studiohsoftware/2WIRELESS/Firmware/photon/PhotonCore/softap.cpp

#include <cstdlib>
#include <algorithm>
#include "wiced.h"
#include "http_server.h"
#include "static_assert.h"
#include "dns_redirect.h"
#include "wiced_security.h"
#include "jsmn.h"
#include "softap.h"
#include "softap_http.h"
#include "dct.h"
#include "ota_flash_hal.h"
#include "spark_protocol_functions.h"
#include "spark_macros.h"
#include "core_hal.h"
#include "rng_hal.h"
#include "ota_flash_hal_stm32f2xx.h"
#include "bytes2hexbuf.h"
#include "spark_wiring_wifi_credentials.h"
#include "mbedtls/aes.h"
#include "device_code.h"
//2WIRELESS
#include "wwd_sdpcm.h"
#include "wwd_wlioctl.h"
#include "wwd_ap_common.h"
#include "rtos.h"
#include "wwd_rtos_interface.h"

#if SOFTAP_HTTP
# include "http_server.h"

# ifndef SOFTAP_HTTP_MAXIMUM_CONNECTIONS
#  define SOFTAP_HTTP_MAXIMUM_CONNECTIONS (10)
# endif // SOFTAP_HTTP_MAXIMUM_CONNECTIONS

# define SOFTAP_HTTP_MAXIMUM_URL_LENGTH 255
#endif // SOFTAP_HTTP

//2WIRELESS
static host_semaphore_type_t wwd_wifi_sleep_flag;

extern WLanSecurityType toSecurityType(wiced_security_t sec);

//2WIRELESS
wwd_result_t disable_ssid_broadcast(int disable)
{
    wiced_buffer_t buffer;
    uint32_t*      data;

	/* Make the AP "hidden" */
	data = (uint32_t*) wwd_sdpcm_get_iovar_buffer( &buffer, (uint16_t) 4, IOVAR_STR_CLOSEDNET );
	CHECK_IOCTL_BUFFER_WITH_SEMAPHORE( data, &wwd_wifi_sleep_flag );
	data[0] = (uint32_t) disable;
	CHECK_RETURN_WITH_SEMAPHORE( wwd_sdpcm_send_iovar( SDPCM_SET, buffer, 0, WWD_AP_INTERFACE ), &wwd_wifi_sleep_flag );
	return WWD_SUCCESS;
}

// This is a copy-paste from spark_wiring_json.h
static size_t json_unescape(char *json, size_t len) {
    char *str = json; // Destination string
    const char* const end = json + len; // End of the source string
    const char *s1 = str; // Beginning of an unescaped sequence
    const char *s = s1;
    while (s != end) {
        if (*s == '\\') {
            if (s != s1) {
                const size_t n = s - s1;
                memmove(str, s1, n); // Shift preceeding characters
                str += n;
                s1 = s;
            }
            ++s;
            if (s == end) {
                return false; // Unexpected end of string
            }
            // if (*s == 'u') { // Arbitrary character, e.g. "\u001f"
            //     ++s;
            //     if (end - s < 4) {
            //         return false; // Unexpected end of string
            //     }
            //     uint32_t u = 0; // Unicode code point or UTF-16 surrogate pair
            //     if (!hexToInt(s, 4, &u)) {
            //         return false; // Invalid escaped sequence
            //     }
            //     if (u <= 0x7f) { // Processing only code points within the basic latin block
            //         *str = u;
            //         ++str;
            //         s1 += 6; // Skip escaped sequence
            //     }
            //     s += 4;
            // } else {
                switch (*s) {
                case '"':
                case '\\':
                case '/':
                    *str = *s;
                    break;
                case 'b': // Backspace
                    *str = 0x08;
                    break;
                case 't': // Tab
                    *str = 0x09;
                    break;
                case 'n': // Line feed
                    *str = 0x0a;
                    break;
                case 'f': // Form feed
                    *str = 0x0c;
                    break;
                case 'r': // Carriage return
                    *str = 0x0d;
                    break;
                default:
                    return false; // Invalid escaped sequence
                }
                ++str;
                ++s;
                s1 = s; // Skip escaped sequence
            // }
        } else {
            ++s;
        }
    }
    if (s != s1) {
        const size_t n = s - s1;
        memmove(str, s1, n); // Shift remaining characters
        str += n;
    }
    return (str - json); // Update string length
}

int resolve_dns_query(const char* query, const char* table)
{
    int result = 0;
    while (*table!=0xFF && *table)
    {
        unsigned len = strlen(table)+1;
        if (!memcmp(query, table, len))
        {
            result = len;
            break;
        }
        table += len;
    }
    return result;
}

/**
 * Override resolution.
 * @param query
 * @return
 */
int dns_resolve_query(const char* query)
{
    int result = dns_resolve_query_default(query);
    if (result<=0)
    {
        const char* valid_queries = (const char*) dct_read_app_data_lock(DCT_DNS_RESOLVE_OFFSET);
        result = resolve_dns_query(query, valid_queries);
        dct_read_app_data_unlock(DCT_DNS_RESOLVE_OFFSET);
    }
    return result;
}

bool is_device_claimed()
{
	return HAL_IsDeviceClaimed(nullptr);
}


/**
 * A command that consumes data from a reader and produces a result to a writer.
 */
class Command {

public:
    /**
     * Executes this command.
     * @param reader    The data supplied to the command.
     * @param writer    The writer that receives the result of the command.
     * @return  A command response code. By convention 0 indicates success.
     */
    virtual int execute(Reader& reader, Writer& writer)=0;
};

/**
 * Base class for commands whose requests and responses are encoded using
 * json.
 */
class JSONCommand : public Command {

protected:

    jsmntok_t * json_tokenise(char *js)
    {
        jsmn_parser parser;
        parser.size = sizeof(parser);
        jsmn_init(&parser, NULL);

        unsigned int n = 64;
        jsmntok_t* tokens = (jsmntok_t*)malloc(sizeof(jsmntok_t) * n);
        if (!tokens) return nullptr;
        int ret = jsmn_parse(&parser, js, strlen(js), tokens, n, NULL);
        while (ret==JSMN_ERROR_NOMEM)
        {
            n = n * 2 + 1;
            jsmntok_t* prev = tokens;
            tokens = (jsmntok_t*)realloc(tokens, sizeof(jsmntok_t) * n);
            if (!tokens) {
            		free(prev);
            		return nullptr;
            }
            ret = jsmn_parse(&parser, js, strlen(js), tokens, n, NULL);
        }
        return tokens;
    }

    bool json_token_streq(const char *js, jsmntok_t *t, const char *s)
    {
        return (strncmp(js + t->start, s, t->end - t->start) == 0
                && strlen(s) == (size_t) (t->end - t->start));
    }

    char* json_token_tostr(char *js, jsmntok_t *t)
    {
        js[t->end] = '\0';
        return js + t->start;
    }

    void write_result_code(Writer& writer, int result) {
        write_char(writer, '{');
        write_json_int(writer, "r", result);
        write_char(writer, '}');
    }

    virtual int parse_request(Reader& reader) { return 0; }

    virtual void produce_response(Writer& writer, int result) {
        write_result_code(writer, result);
    }

    /**
     * The core processing for this command. Consumes the request object and produces
     * the response.
     * @return The command result code to return from execute().
     */
    virtual int process() { return 0; }

    void write_char(Writer& w, char c) {
        w.write((uint8_t*)&c, 1);
    }

    void write_quoted_string(Writer& out, const char* s) {
        write_char(out, '"');
        out.write(s);
        write_char(out, '"');
    }

    void write_json_string(Writer& out, const char* name, const char* value) {
        write_quoted_string(out, name);
        write_char(out, ':');
        write_quoted_string(out, value);
    }

    char* int_to_ascii(int val, char* buf, int i) {
        buf[--i] = 0;
        bool negative = val < 0;
        if (negative) {
            val = -val;
        }
        buf[--i] = (val % 10) + '0';
        val /= 10;
        for(; val && i ; val /= 10) {
            buf[--i] = (val % 10) + '0';
        }
        if (negative)
            buf[--i] = '-';
        return &buf[i];
    }

    void write_json_int(Writer& out, const char* name, int value) {
        char buf[20];
        write_quoted_string(out, name);
        write_char(out, ':');
        out.write(int_to_ascii(value, buf, 20));
    }

public:

    virtual int execute(Reader& reader, Writer& writer)
    {
        int result = parse_request(reader);
        if (!result) {
            result = process();
            produce_response(writer, result);
        }
        return result;
    }
};


#define JSON_DEBUG(x)

/**
 * A command that parses a JSON request.
 */

class JSONRequestCommand : public JSONCommand {

protected:

	/**
	 * Template method allowing subclasses to handle the parsed json keys.
	 * @param index The index into the array of keys passed to parse_json_requet of the key that has been matched.
	 */
    virtual bool parsed_key(unsigned index)=0;

    /**
     * Template methods allowing subclasses to handle the parsed JSON values.
     * @param index	the key index this value belongs to
     * @param t		the jsmn token
     * @param value	The string value.
     *
     * Note that the t and value parameters have a lifetime only for the duration of the method.
     * They should not be stored for later use.
     */
    virtual bool parsed_value(unsigned index, jsmntok_t* t, char* value)=0;

    int parse_json_request(Reader& reader, const char* const keys[], const jsmntype_t types[], unsigned count) {

        int result = -1;
    		char* js = reader.fetch_as_string();
        if (js)
        {
			jsmntok_t *tokens = json_tokenise(js);
			if (tokens)
			{
				enum parse_state { START, KEY, VALUE, SKIP, STOP };

				parse_state state = START;
				jsmntype_t expected_type = JSMN_OBJECT;

				result = 0;
				int key = -1;

				for (size_t i = 0, j = 1; j > 0; i++, j--)
				{
					jsmntok_t *t = &tokens[i];
					if (t->type == JSMN_ARRAY || t->type == JSMN_OBJECT)
						j += t->size * 2;

					switch (state)
					{
						case START:
							state = KEY;
							break;

						case KEY:
							state = VALUE;
							key = -1;
							for (size_t i = 0; i < count; i++)
							{
								if (json_token_streq(js, t, keys[i]))
								{
									expected_type = types[i];
									if (parsed_key(i)) {
										key = i;
										JSON_DEBUG( ( "key: %s %d %d\n", keys[i], i, (int)expected_type ) );
									}
								}
							}
							if (key==-1) {
								JSON_DEBUG( ( "unknown key: %s\n", json_token_tostr(js, t) ) );
								result = -1;
							}
							break;

						case VALUE:
							if (key!=-1) {
								if (t->type != expected_type) {
									result = -1;
									JSON_DEBUG( ( "type mismatch\n" ) );
								}
								else {
									char *str = json_token_tostr(js, t);
									if (!parsed_value(key, t, str))
										result = -1;
								}
							}
							state = KEY;
							break;

						case STOP: // Just consume the tokens
							break;

						default:
							result = -1;
					}
				}
				free(tokens);
			}
			free(js);
        }
        return result;
    }
};


class VersionCommand : public JSONCommand {

public:
    void produce_response(Writer& out, int result) {
        out.write("{\"v\":2}");
    }
};

struct ScanEntry {
    char ssid[33];
    uint8_t done;
    int32_t rssi;
    int32_t security;
    int32_t channel;
    int32_t max_data_rate;
};

class ScanAPCommand : public JSONCommand {
    wiced_queue_t queue_;

    // these can be quite large, so allocate on the heap
    ScanEntry read_;
    ScanEntry write_;

public:
    ScanAPCommand()
    {
    }

    /**
     * Initializes the scan queue, and start a scan using the WICED wifi scan api.
     *
     */
    int process() {
        int result = wiced_rtos_init_queue(&queue_, NULL, sizeof(ScanEntry), 5);
        if (!result) {
            result = wiced_wifi_scan_networks(scan_handler, this);
            if (result)
                wiced_rtos_deinit_queue(&queue_);
        }
        return result;
    }

    void produce_response(Writer& out, const int result) {
        out.write("{\"scans\":[");
        bool first = true;
        ScanEntry& entry = read_;
        while (!result && !wiced_rtos_pop_from_queue(&queue_, &entry, WICED_NEVER_TIMEOUT)) {
            if (entry.done)
                break;
            if (!*entry.ssid)
                continue;
            if (first)
                first = false;
            else
                write_char(out, ',');
            write_char(out, '{');
            write_json_string(out, "ssid", entry.ssid);
            write_char(out, ',');
            write_json_int(out, "rssi", entry.rssi);
            write_char(out, ',');
            write_json_int(out, "sec", entry.security);
            write_char(out, ',');
            write_json_int(out, "ch", entry.channel);
            write_char(out, ',');
            write_json_int(out, "mdr", entry.max_data_rate);
            write_char(out, '}');
        }
        out.write("]}");
        wiced_rtos_deinit_queue(&queue_);
    }

    static wiced_result_t scan_handler(wiced_scan_handler_result_t* malloced_scan_result)
    {
        ScanAPCommand& cmd = *(ScanAPCommand*)malloced_scan_result->user_data;
        malloc_transfer_to_curr_thread( malloced_scan_result );
        ScanEntry& entry = cmd.write_;
        memset(&entry, 0, sizeof(entry));
        if (malloced_scan_result->status == WICED_SCAN_INCOMPLETE)
        {
            wiced_scan_result_t& ap_details = malloced_scan_result->ap_details;
            unsigned ssid_len = ap_details.SSID.length > 32 ? 32 : ap_details.SSID.length;
            memcpy(entry.ssid, ap_details.SSID.value, ssid_len);
            entry.ssid[ssid_len] = 0;
            entry.rssi = ap_details.signal_strength;
            entry.security = ap_details.security;
            entry.channel = ap_details.channel;
            entry.max_data_rate = ap_details.max_data_rate;
        }
        else
        {
            entry.done = 1;
        }
        wiced_rtos_push_to_queue(&cmd.queue_, &entry, WICED_WAIT_FOREVER);
        free(malloced_scan_result);
        return WICED_SUCCESS;
    }
};

struct ConfigureAP {
    int32_t index;
    char ssid[33];
    char passcode[65];
    int32_t security;
    int32_t channel;
};


uint8_t hex_nibble(unsigned char c) {
    if (c<'0')
        return 0;
    if (c<='9')
        return c-'0';
    if (c<='Z')
        return c-'A'+10;
    if (c<='z')
        return c-'a'+10;
    return 0;
}

size_t hex_decode(uint8_t* buf, size_t len, const char* hex) {
    unsigned char c = '0'; // any non-null character
    size_t i;
    for (i=0; i<len && c; i++) {
        uint8_t b;
        if (!(c = *hex++))
            break;
        b = hex_nibble(c)<<4;
        if (c) {
            c = *hex++;
            b |= hex_nibble(c);
        }
        *buf++ = b;
    }
    return i;
}

/**
 *
 * @param hex_encoded   The hex_encoded encrypted data
 * The plaintext is stored in hex_encoded
 */
int decrypt(char* plaintext, int max_plaintext_len, char* hex_encoded_ciphertext) {
    const size_t len = 256;
    uint8_t buf[len];
    hex_decode(buf, len, hex_encoded_ciphertext);

    // reuse the hex encoded buffer
    const uint8_t *key = fetch_device_private_key(1); // fetch and lock private key data
    int plaintext_len = decrypt_rsa(buf, key, (uint8_t*)plaintext, max_plaintext_len);
    fetch_device_private_key(0); // unlock private key data
    return plaintext_len;
}

/**
 * Connects to an access point using the given credentials and signals
 * soft-ap process complete.
 */
class ConfigureAPCommand : public JSONRequestCommand {

	/**
	 * Receives the data from parsing the json.
	 */
    spark::WiFiAllocatedCredentials credentials;

    static const char* KEY[12];
    static const int OFFSET[];
    static const jsmntype_t TYPE[];

    std::unique_ptr<char[]> ekey_;

    int decrypt_result;

    int save_credentials() {
        WLanCredentials creds = credentials.getHalCredentials();
        if (creds.private_key && creds.private_key_len) {
            creds.private_key_len = decrypt_private_key(creds.private_key, creds.private_key_len);
        }
        return decrypt_result<0 ? decrypt_result :
            wlan_set_credentials(&creds);
    }

protected:

    virtual bool parsed_key(unsigned index) {
        return true;
    }

    int decrypt_private_key(const uint8_t* pkey, int len) {
        if (!(ekey_ && pkey && len))
            return 0;

        const size_t block_size = 16;
        uint8_t buf[block_size];
        const uint8_t* key = (const uint8_t*)ekey_.get();
        uint8_t* iv = (uint8_t*)ekey_.get() + block_size;

        mbedtls_aes_context ctx = {0};
        mbedtls_aes_setkey_dec(&ctx, key, 128);

        uint8_t* bptr = (uint8_t*)pkey;

        for (uint8_t* ptr = (uint8_t*)pkey; ptr - pkey < len; ptr += block_size * 2) {
            hex_decode(buf, block_size, (const char*)ptr);
            mbedtls_aes_crypt_cbc(&ctx, MBEDTLS_AES_DECRYPT, block_size, iv, buf, bptr);
            bptr += block_size;
        }

        decrypt_result = 1;

        return (len / 2);
        }

    virtual bool parsed_value(unsigned key, jsmntok_t* t, char* str) {
        std::unique_ptr<char[]> tmp;
        switch(key) {
            case 0:
            // idx
            break;
            case 1:
            // ssid
            if (t->type == JSMN_STRING) {
                credentials.setSsid(str);
            }
            break;
            case 2:
            // pwd
            if (t->type == JSMN_STRING) {
#define USE_PWD_ENCRYPTION 1
#if USE_PWD_ENCRYPTION
                size_t len = strlen(str);
                if (len / 2) {
                    tmp.reset(new (std::nothrow) char[len / 2 + 1]);
                    if (tmp) {
                        memset(tmp.get(), 0, len / 2 + 1);
                        decrypt_result = decrypt((char*)tmp.get(), len, str);
                        JSON_DEBUG( ( "Decrypted password %s\n", (char*)tmp));
                        str = tmp.get();
                    }
                }
#endif
                credentials.setPassword(str);
        }
            break;
            case 3:
            // ch
            credentials.setChannel(atoi(str));
            break;
            case 4:
            // sec
            // Why are we receiving WICED-specific security type here?
            credentials.setSecurity((WLanSecurityType)toSecurityType((wiced_security_t)atoi(str)));
            break;
            case 5:
            // eap
            credentials.setEapType((WLanEapType)atoi(str));
            break;
            case 6:
            // outer identity
            if (t->type == JSMN_STRING) {
                credentials.setOuterIdentity(str);
        }
            break;
            case 7:
            // inner identity
            if (t->type == JSMN_STRING) {
                credentials.setInnerIdentity(str);
            }
            break;
            case 8:
            // certificate
            if (t->type == JSMN_STRING) {
                size_t len = json_unescape(str, strlen(str));
                credentials.setClientCertificate((const uint8_t*)str, len + 1);
            }
            break;
            case 9:
            // encryption key
            if (t->type == JSMN_STRING) {
                size_t len = strlen(str);
                if (len / 2) {
                    tmp.reset(new (std::nothrow) char[len / 2 + 1]);
                    if (tmp) {
                        memset(tmp.get(), 0, len / 2 + 1);
                        decrypt_result = decrypt((char*)tmp.get(), len, str);
                        ekey_ = std::move(tmp);
                    }
                }
            }
            break;
            case 10:
            // private key
            if (t->type == JSMN_STRING) {
                size_t len = strlen(str);
                credentials.setPrivateKey((const uint8_t*)str, len + 1);
                // Just in case set the password as well, as there is a check somewhere that will
                // set security to Open if there is no password.
                credentials.setPassword("1");
            }
            break;
            case 11:
            // root ca
            if (t->type == JSMN_STRING) {
                size_t len = json_unescape(str, strlen(str));
                credentials.setRootCertificate((const uint8_t*)str, len + 1);
            }
            break;
        }
        return true;
    }

    int parse_request(Reader& reader) {
        decrypt_result = 0;
        credentials.reset();
        return parse_json_request(reader, KEY, TYPE, arraySize(KEY));
    }

    /**
     * Write the requested AP details to DCT
     * @return
     */
    int process() {
        return save_credentials();
    }

};

const char* ConfigureAPCommand::KEY[12] = {"idx","ssid","pwd","ch","sec",
                                           "eap","oi","ii","crt","ek","key","ca"};
const jsmntype_t ConfigureAPCommand::TYPE[] = { JSMN_PRIMITIVE, JSMN_STRING, JSMN_STRING,
                                                JSMN_PRIMITIVE, JSMN_PRIMITIVE, JSMN_PRIMITIVE,
                                                JSMN_STRING, JSMN_STRING, JSMN_STRING,
                                                JSMN_STRING, JSMN_STRING, JSMN_STRING };


class ConnectAPCommand : public JSONCommand {
    int index;
    wiced_semaphore_t* signal_complete_;
    void (*softap_complete_)();
    int responseCode;
public:
    ConnectAPCommand(wiced_semaphore_t* signal_complete, void (*softap_complete)()) {
        signal_complete_ = signal_complete;
        softap_complete_ = softap_complete;
    }

protected:
    // todo - parse index

    int process() {
        int result = 1;
        if (signal_complete_!=NULL) {
            wiced_rtos_set_semaphore(signal_complete_);
            result = 0;
        }
        return result;
    }

    void produce_response(Writer& writer, int result) {
        write_result_code(writer, result);
        if (softap_complete_)
            softap_complete_();
    }
};

class DeviceIDCommand : public JSONCommand {

    char device_id[25];

public:
    DeviceIDCommand() {}

    static void get_device_id(char buffer[25]) {
        bytes2hexbuf((const uint8_t*)0x1FFF7A10, 12, buffer);
        buffer[24] = 0;
    }

protected:
    int process() {
        memset(device_id, 0, sizeof(device_id));
        get_device_id(device_id);
        return 0;
    }

    void produce_response(Writer& writer, int result) {
        write_char(writer, '{');
        write_json_string(writer, "id", device_id);
        write_char(writer, ',');
        write_json_string(writer, "c", is_device_claimed() ? "1" : "0");
        write_char(writer, '}');
    }
};

class PublicKeyCommand : public JSONCommand {

protected:

    int process() {
        return 0;
    }

    void produce_response(Writer& writer, int result) {
        // fetch public key
        const int length = EXTERNAL_FLASH_SERVER_PUBLIC_KEY_LENGTH;
        const uint8_t* data = fetch_device_public_key(1); // fetch and lock public key data
        write_char(writer, '{');
        if (data) {
            writer.write("\"b\":\"");
            for (unsigned i=length; i-->0; ) {
                uint8_t v = *data++;
                write_char(writer, ascii_nibble(v>>4));
                write_char(writer, ascii_nibble(v&0xF));
            }
            write_char(writer, '"');
            write_char(writer, ',');
        }
        else {
            result = 1;
        }

        fetch_device_public_key(0); // unlock public key data

        write_json_int(writer, "r", result);
        write_char(writer, '}');
    }
};


class SetValueCommand  : public JSONRequestCommand {

	static const unsigned MAX_KEY_LEN = 3;
	static const unsigned MAX_VALUE_LEN = 64;

    static const char* const KEY[2];
    static const jsmntype_t TYPE[2];

    char key[MAX_KEY_LEN+1];
    char value[MAX_VALUE_LEN+1];

protected:

    virtual bool parsed_key(unsigned index) {
        return true;
    }

    inline void assign(char* target, const char* value, unsigned len) {
    		strncpy(target, value, len);
    		target[len-1] = '\0';
    }

    virtual bool parsed_value(unsigned index, jsmntok_t* t, char* value) {
        if (index==0)     // key
        		assign(this->key, value, MAX_KEY_LEN);
        else
        		assign(this->value, value, MAX_VALUE_LEN);
        return true;
    }

    int parse_request(Reader& reader) {
        key[0] = 0; value[0] = 0;
        return parse_json_request(reader, KEY, TYPE, arraySize(KEY));
    }

    int process() {
        int result = -1;
        if (*key && *value) {
            if (!strcmp(key,"cc")) {
                result = HAL_Set_Claim_Code(value);
            }
        }
        return result;
    }
};

const char* const SetValueCommand::KEY[2] = { "k", "v" };
const jsmntype_t SetValueCommand::TYPE[2] = { JSMN_STRING, JSMN_STRING };

struct AllSoftAPCommands {
    VersionCommand version;
    DeviceIDCommand deviceID;
    ScanAPCommand scanAP;
    ConfigureAPCommand configureAP;
    ConnectAPCommand connectAP;
    PublicKeyCommand publicKey;
    SetValueCommand setValue;
    AllSoftAPCommands(wiced_semaphore_t* complete, void (*softap_complete)()) :
        connectAP(complete, softap_complete) {}
};

const int MAX_SSID_PREFIX_LEN = 25;

bool fetch_or_generate_ssid_prefix(device_code_t* SSID) {
    const uint8_t* prefix = (const uint8_t*)dct_read_app_data_lock(DCT_SSID_PREFIX_OFFSET);
    uint8_t len = *prefix;
    bool generate = (!len || len>MAX_SSID_PREFIX_LEN);
    if (generate) {
        dct_read_app_data_unlock(DCT_SSID_PREFIX_OFFSET);
        strcpy((char*)SSID->value, "Photon");
        SSID->length = 6;
        dct_write_app_data(SSID, DCT_SSID_PREFIX_OFFSET, SSID->length+1);
    }
    else {
        memcpy(SSID, prefix, DCT_SSID_PREFIX_SIZE);
        dct_read_app_data_unlock(DCT_SSID_PREFIX_OFFSET);
    }
    if (SSID->length>MAX_SSID_PREFIX_LEN)
        SSID->length = MAX_SSID_PREFIX_LEN;
    return generate;
}

extern "C" wiced_ip_setting_t device_init_ip_settings;

/**
 * Manages the soft access point.
 */
class SoftAPController {
    wiced_semaphore_t complete;
    dns_redirector_t dns_redirector;

    wiced_result_t setup_soft_ap_credentials() {

        wiced_config_soft_ap_t expected;
        memset(&expected, 0, sizeof(expected));
        fetch_or_generate_setup_ssid((device_code_t*)&expected.SSID);

        expected.channel = 11;
        expected.details_valid = WICED_TRUE;

        wiced_config_soft_ap_t* soft_ap;
        wiced_result_t result = wiced_dct_read_lock( (void**) &soft_ap, WICED_FALSE, DCT_WIFI_CONFIG_SECTION, OFFSETOF(platform_dct_wifi_config_t, soft_ap_settings), sizeof(wiced_config_soft_ap_t) );
        if (result == WICED_SUCCESS)
        {
            if (memcmp(&expected, soft_ap, sizeof(expected))) {
                wiced_dct_read_unlock( soft_ap, WICED_FALSE );
                result = wiced_dct_write(&expected, DCT_WIFI_CONFIG_SECTION, OFFSETOF(platform_dct_wifi_config_t, soft_ap_settings), sizeof(wiced_config_soft_ap_t));
            } else {
                wiced_dct_read_unlock( soft_ap, WICED_FALSE );
            }
        }
		
        return result;
    }

public:

    wiced_semaphore_t& complete_semaphore() {
        return complete;
    }

    wiced_result_t start() {
        wiced_result_t result;
        if (!(result=wiced_rtos_init_semaphore(&complete)))
            if (!(result=setup_soft_ap_credentials()))
                if (!(result=wiced_network_up( WICED_AP_INTERFACE, WICED_USE_INTERNAL_DHCP_SERVER, &device_init_ip_settings )))
                    if (!(result=wiced_dns_redirector_start( &dns_redirector, WICED_AP_INTERFACE )))
                        result = WICED_SUCCESS;
        return result;
    }

    void waitForComplete() {
        wiced_rtos_get_semaphore(&complete, WICED_WAIT_FOREVER);
    }

    void signalComplete() {
        wiced_rtos_set_semaphore(&complete);
    }

    void stop() {

        /* Cleanup DNS server */
        wiced_dns_redirector_stop(&dns_redirector);

        /* Turn off AP */
        wiced_network_down( WICED_AP_INTERFACE );

        signalComplete();
        wiced_rtos_deinit_semaphore(&complete);
    }
};

class Dispatcher {
public:
    void start() {};
    void stop() {};
};

static void tcp_write(Writer* w, const uint8_t *buf, size_t count) {
    wiced_tcp_stream_t* tcp_stream = (wiced_tcp_stream_t*)w->state;
    wiced_tcp_stream_write(tcp_stream, buf, count);
}

static int tcp_read(Reader* r, uint8_t *buf, size_t count) {
    wiced_tcp_stream_t* tcp_stream = (wiced_tcp_stream_t*)r->state;
    int result = wiced_tcp_stream_read(tcp_stream, buf, count, WICED_NEVER_TIMEOUT);
    return result==WICED_SUCCESS ? count : (result < 0 ? result : -result);
}

static void tcp_stream_writer(Writer& w, wiced_tcp_stream_t* stream) {
    w.callback = tcp_write;
    w.state = stream;
}

static void tcp_stream_reader(Reader& r, wiced_tcp_stream_t* stream) {
    r.bytes_left = SIZE_MAX;
    r.callback = tcp_read;
    r.state = stream;
}

int read_from_buffer(Reader* r, uint8_t* target, size_t length) {
    memcpy(target, r->state, length);
    r->state = ((uint8_t*)r->state)+length;
    return length;
}

void reader_from_buffer(Reader* r, const uint8_t* buffer, size_t length)
{
    r->bytes_left = length;
    r->callback = read_from_buffer;
    r->state = (void*)buffer;
}


void cleanup_http_body(wiced_http_message_body_t* body)
{
    if (body->user)
    {
        wiced_packet_delete((wiced_packet_t*)body->user);
        body->user = NULL;
    }
}

int read_from_http_body_part(wiced_http_message_body_t* body, uint8_t* target, size_t length)
{
    // first read from the data already read in the body
    if (body->message_data_length)
    {
        if (length>body->message_data_length)
            length = body->message_data_length;

        memcpy(target, body->data, length);
        body->message_data_length -= length;
        body->data += length;
        return length;
    }
    else if (body->total_message_data_remaining)
    {
        cleanup_http_body(body);

        // fetch the next packet - we assume length is large enough to hold the packet content
        // which is the case since we are retrieving the entire content in Reader::fetch_as_string())
        wiced_packet_t* packet = NULL;
        wiced_result_t result = wiced_tcp_receive(body->socket, &packet, 3000);
        if (result)
            return -1;

        body->user = packet;         // ensure we clean up the packet
        uint16_t packet_length;
        uint16_t available_data_length;
        uint32_t offset =0;
        uint8_t* data;

        do
        {
            result = wiced_packet_get_data(packet, offset, &data, &packet_length, &available_data_length);
            if (result)
                return -1;

            if (length>available_data_length)
                length = available_data_length;
            else
                available_data_length = length;

            uint32_t tocopy = std::min(length, size_t(packet_length));
            memcpy(target, data, tocopy);
            length -= tocopy;
            target += tocopy;
            offset += packet_length;
        }
        while (length && offset < available_data_length);

        body->total_message_data_remaining -= available_data_length;
        return available_data_length;
    }
    else
        return -1;
}

/**
 * This implementation takes some shortcuts since it's just a placeholder until
 * WICED implements http based on streams rather than packets.
 * This function relies upon the Reader::fetch_as_string() call that reads
 * the entire content in one call.
 * @param r
 * @param target
 * @param length
 * @return
 */
int read_from_http_body(Reader* r, uint8_t* target, size_t length) {
    size_t read = 0;
    wiced_http_message_body_t* body = (wiced_http_message_body_t*)r->state;
    while (read<length)
    {
        int block = read_from_http_body_part(body, target, length-read);
        if (block<0)
            break;
        target += block;
        read += block;
    }
    return read;
}

void reader_from_http_body(Reader* r, wiced_http_message_body_t* body)
{
    if (false && body->total_message_data_remaining==0)
    {
        reader_from_buffer(r, (uint8_t*)body->data, body->message_data_length);
    }
    else
    {
        r->bytes_left = body->message_data_length + body->total_message_data_remaining;
        r->callback = read_from_http_body;
        r->state = body;
    }
}

#if SOFTAP_HTTP
extern "C" wiced_http_page_t soft_ap_http_pages[];

extern const char* SOFT_AP_MSG;
extern "C" void default_page_handler(const char* url, ResponseCallback* cb, void* cbArg, Reader* body, Writer* result, void* reserved)
{
	if (strcmp(url,"/index")) {
		cb(cbArg, 0, 404, 0, 0);	// not found
	}
	else {
		Header h("Location: /hello\r\n");
		cb(cbArg, 0, 301, "text/plain", &h);
	}
}


static void http_write(Writer* w, const uint8_t *buf, size_t count) {
    wiced_http_response_stream_t* stream = (wiced_http_response_stream_t*)w->state;
    wiced_http_response_stream_write(stream, buf, count);
}

static void http_stream_writer(Writer& w, wiced_http_response_stream_t* stream) {
    w.callback = http_write;
    w.state = stream;
}

/**
 * Maps from the status code as an integer to the WICED HTTP server codes.
 */
http_status_codes_t status_from_code(uint16_t response)
{
	switch (response) {
	case 200:
		return HTTP_200_TYPE;
	case 204:
		return HTTP_204_TYPE;
	case 207:
		return HTTP_207_TYPE;
	case 301:
		return HTTP_301_TYPE;
	case 400:
	default:
		return HTTP_400_TYPE;
	case 403:
		return HTTP_403_TYPE;
	case 404:
		return HTTP_404_TYPE;
	case 405:
		return HTTP_405_TYPE;
	case 406:
		return HTTP_406_TYPE;
	case 412:
		return HTTP_412_TYPE;
	case 415:
		return HTTP_415_TYPE;
	case 429:
		return HTTP_429_TYPE;
	case 444:
		return HTTP_444_TYPE;
	case 470:
		return HTTP_470_TYPE;
	case 500:
		return HTTP_500_TYPE;
	case 504:
		return HTTP_504_TYPE;
	}
}

int writeHeader(void* cbArg, uint16_t flags, uint16_t responseCode, const char* mimeType, Header* header)
{
	const char* header_list = nullptr;
	if (header && header->size) {
		header_list = header->header_list;
	}

   return wiced_http_response_stream_write_header( (wiced_http_response_stream_t*)cbArg, status_from_code(responseCode),
		   CHUNKED_CONTENT_LENGTH, HTTP_CACHE_DISABLED, http_server_get_mime_type(mimeType), header_list);
}

struct HTTPRequest {
    char* url;
    wiced_http_response_stream_t* stream;
    uint8_t* buffer;
    bool alloced;
    size_t length;
    size_t total_length;
    // const char* url_query_string;

    HTTPRequest()
        : url{nullptr},
          buffer{nullptr},
          alloced{false} {
        reset();
    }

    ~HTTPRequest() {
        reset();
    }

    bool init(const char* u, wiced_http_response_stream_t* s, wiced_http_message_body_t* b) {
        stream = s;
        if (b->message_data_length != 0 && b->total_message_data_remaining == 0) {
            url = nullptr;
            // Single packet
            total_length = length = b->message_data_length;
            buffer = (uint8_t*)b->data;
            alloced = false;
        } else if (b->total_message_data_remaining) {
            // Multi-packet
            buffer = (uint8_t*)malloc(b->total_message_data_remaining + b->message_data_length);
            if (buffer == nullptr) {
                reset();
                return false;
            }
            alloced = true;
            length = b->message_data_length;
            total_length = length + b->total_message_data_remaining;
            if (length > 0) {
                memcpy(buffer, b->data, length);
            }

            const size_t l = strlen(u) + 1;
            url = (char*)calloc(1, std::min(l, (size_t)SOFTAP_HTTP_MAXIMUM_URL_LENGTH));
            if (url == nullptr) {
                reset();
                return false;
            }
            memcpy(url, u, std::min(l, (size_t)SOFTAP_HTTP_MAXIMUM_URL_LENGTH - 1));
        }

        return true;
    }

    bool append(wiced_http_message_body_t* b) {
        memcpy(buffer + length, b->data, b->message_data_length);
        length += b->message_data_length;
        return true;
    }

    bool matches(const char* u, wiced_http_response_stream_t* s, wiced_http_message_body_t* b) const {
        if (s == nullptr || b == nullptr) {
            return false;
        }

        if (stream == nullptr || s != stream) {
            return false;
        }

        if ((b->message_data_length + b->total_message_data_remaining + length) != total_length) {
            return false;
        }

        return true;
    }

    bool ready() const {
        return !empty() && length == total_length;
    }

    void reset() {
        if (buffer && alloced) {
            free(buffer);
        }
        buffer = nullptr;
        alloced = false;
        stream = nullptr;
        length = 0;
        total_length = 0;
        if (url) {
            free(url);
        }
        url = nullptr;
    }

    Reader reader() {
        Reader r;
        reader_from_buffer(&r, buffer, length);
        return r;
    }

    Writer writer() {
        Writer w;
        http_stream_writer(w, stream);
        return w;
    }

    bool empty() const {
        return (url == nullptr && stream == nullptr && buffer == nullptr && length == 0 && total_length == 0);
    }
};

class HTTPDispatcher {
    wiced_http_server_t server;

    wiced_http_page_t page[10];

    static HTTPRequest* reqs;

    void setCommand(unsigned index, Command& cmd) {
        page[index].url_content.dynamic_data.generator = handle_command;
        page[index].url_content.dynamic_data.arg = &cmd;
    }

public:
    HTTPDispatcher(AllSoftAPCommands& commands) {
        memset(&server, 0, sizeof(server));
        memcpy(page, soft_ap_http_pages, sizeof(page));
        setCommand(2, commands.version);
        setCommand(3, commands.deviceID);
        setCommand(4, commands.scanAP);
        setCommand(5, commands.configureAP);
        setCommand(6, commands.connectAP);
        setCommand(7, commands.publicKey);
        setCommand(8, commands.setValue);
        page[9].url_content.dynamic_data.generator = handle_app_renderer;
        page[9].url_content.dynamic_data.arg = (void*)softap_get_application_page_handler();
    }

    void start() {
        reqs = new HTTPRequest[SOFTAP_HTTP_MAXIMUM_CONNECTIONS];
        wiced_http_server_start(&server, 80, SOFTAP_HTTP_MAXIMUM_CONNECTIONS, page, WICED_AP_INTERFACE, 1024*4);
    }

    void stop() {
        wiced_http_server_stop(&server);
        delete[] reqs;
        reqs = nullptr;
    }

    template <typename F>
    static HTTPRequest* for_request(F&& f) {
        if (reqs == nullptr) {
            return nullptr;
        }

        for(HTTPRequest* r = reqs; r < reqs + SOFTAP_HTTP_MAXIMUM_CONNECTIONS; r++) {
            if (f(r) == true) {
                return r;
            }
        }

        return nullptr;
    }

    static int32_t handle_request(const char* url, const char* url_query_string, wiced_http_response_stream_t* stream, void* arg, wiced_http_message_body_t* http_data, bool isCmd) {
        int result = WICED_SUCCESS;
        HTTPRequest* req = for_request([&](HTTPRequest* r) {
            return r->matches(url, stream, http_data);
        });
        if (req == nullptr) {
            req = for_request([&](HTTPRequest* r) {
                if (r->empty()) {
                    if (r->init(url, stream, http_data)) {
                        return true;
                    }
                }
                return false;
            });
            if (req == nullptr) {
                // Try to match stream only
                req = for_request([&](HTTPRequest* r) {
                    return r->stream == stream;
                });
                if (req == nullptr) {
                    // Error
                    wiced_http_response_stream_write_header(stream, HTTP_500_TYPE, NO_CONTENT_LENGTH, HTTP_CACHE_DISABLED, MIME_TYPE_TEXT_HTML, nullptr);
                    return WICED_ERROR;
                }
                // There shouldn't be two active connections with the same response stream, reuse
                req->reset();
            }
        } else {
            req->append(http_data);
        }

        if (req->ready()) {
            // Process request
            wiced_http_response_stream_enable_chunked_transfer(req->stream);
            stream->cross_host_requests_enabled = WICED_TRUE;

            Reader r = req->reader();
            Writer w = req->writer();
            if (isCmd) {
                Command* cmd = (Command*)arg;
                wiced_http_response_stream_write_header(req->stream, HTTP_200_TYPE, CHUNKED_CONTENT_LENGTH, HTTP_CACHE_DISABLED, MIME_TYPE_JSON, nullptr);
                result = cmd->execute(r, w);
            } else {
                PageProvider* p = (PageProvider*)arg;
                if (p) {
                    char* baseurl = (char*)(req->url ? req->url : url);
                    if (baseurl != nullptr) {
                        const size_t baseurl_len = strlen(baseurl);
                        // Restore full query string
                        if (url_query_string != nullptr &&
                            strlen(url_query_string) && url_query_string == (baseurl + baseurl_len + 1)) {
                            baseurl[baseurl_len] = '?';
                            p(baseurl, &writeHeader, req->stream, &r, &w, nullptr);
                            baseurl[baseurl_len] = '\0';
                        } else {
                            p(baseurl, &writeHeader, req->stream, &r, &w, nullptr);
                        }
                    }
                }
            }
            // We need to deactivate chunked transfer mode here
            // in order to signal to client that there'll be no more data: "0\r\n\r\n"
            wiced_http_response_stream_disable_chunked_transfer(req->stream);
            req->reset();
        }
        return result;
    }

    static int32_t handle_command(const char* url, const char* url_query_string, wiced_http_response_stream_t* stream, void* arg, wiced_http_message_body_t* http_data) {
        return handle_request(url, url_query_string, stream, arg, http_data, true);
    }

    static int32_t handle_app_renderer(const char* url, const char* url_query_string, wiced_http_response_stream_t* stream, void* arg, wiced_http_message_body_t* http_data) {
        return handle_request(url, url_query_string, stream, arg, http_data, false);
    }

};

HTTPRequest* HTTPDispatcher::reqs = nullptr;
#endif


/**
 * Parses a very simple protocol for sending command requests over a stream
 * and dispatches the commands to a AllSoftAPCommands instance.
 */
class SimpleProtocolDispatcher
{
    AllSoftAPCommands& commands_;

    int readChar(Reader& reader, char* c) {
        uint8_t tmp = 0;
        int result = reader.read(&tmp, 1);
        if (result >= 0) {
            *c = tmp;
    }
        return result;
    }

    Command* commandForName(const char* name) {
        Command* cmd = NULL;
        if (name) {
            // todo - create an array of commands and names and do a scan!
            if (!strcmp("version", name))
                cmd = &commands_.version;
            else if (!strcmp("device-id", name))
                cmd = &commands_.deviceID;
            else if (!strcmp("scan-ap", name))
                cmd = &commands_.scanAP;
            else if (!strcmp("configure-ap", name))
                cmd = &commands_.configureAP;
            else if (!strcmp("connect-ap", name))
                cmd = &commands_.connectAP;
            else if (!strcmp("public-key", name))
                cmd = &commands_.publicKey;
            else if (!strcmp("set", name))
                cmd = &commands_.setValue;
            else if (!strcmp("ant-internal", name))
                wwd_wifi_select_antenna(WICED_ANTENNA_1);
            else if (!strcmp("ant-external", name))
                wwd_wifi_select_antenna(WICED_ANTENNA_2);
        }
        return cmd;
    }

public:
    SimpleProtocolDispatcher(AllSoftAPCommands& commands) : commands_(commands) {}

    int handle(Reader& reader, Writer& writer) {
        char name[30];
        int requestLength = 0;
        int idx = 0;
        int result = -1;

        while (idx<30) {
            char c = 0;
            result = readChar(reader, &c);
            if (!c || c=='\n' || result < 0)
                break;
            name[idx++] = c;
        }
        name[idx] = 0;
        WPRINT_APP_INFO( ( "Fetched name '%s'\n", name ) );

        for (;;) {
            char c = 0;
            result = readChar(reader, &c);
            if (c=='\n' || result < 0)
                break;
            requestLength = requestLength * 10 + c-'0';
        }

        WPRINT_APP_INFO( ( "Request length %d\n", requestLength) );

        // todo - keep reading until a \n\n is encountered.
        bool seenNewline = true;
        for (;;) {
            char c = 0;
            result = readChar(reader, &c);
            if (result < 0)
                break;
            if (c=='\n') {
                if (seenNewline)
                    break;
                else
                    seenNewline = true;
            }
            else
                seenNewline = false;
        }

        Command* cmd = commandForName(name);
        if (cmd) {
            WPRINT_APP_INFO( ( "invoking command %s\n", name ) );
            reader.bytes_left = requestLength;
            // allow for some protocol preamble before the payload
            writer.write("\n\n");
            result = cmd->execute(reader, writer);
            WPRINT_APP_INFO( ( "invoking command %s done\n", name ) );
        }
        else {
            WPRINT_APP_INFO( ( "Unknown command '%s'\n", name ) );
        }
        return result;
    }
};


class SerialDispatcher {
    uint8_t             rx_data[64];
    wiced_uart_config_t uart_config;
    wiced_ring_buffer_t rx_buffer;

public:
    SerialDispatcher(SimpleProtocolDispatcher& dispatcher) {}

    void start() {
#if 0
        uart_config =
        {
            .baud_rate    = 115200,
            .data_width   = DATA_WIDTH_8BIT,
            .parity       = NO_PARITY,
            .stop_bits    = STOP_BITS_1,
            .flow_control = FLOW_CONTROL_DISABLED,
        };

        ring_buffer_init(&rx_buffer, rx_data, RX_BUFFER_SIZE );
        wiced_uart_init( STDIO_UART, &uart_config, &rx_buffer );
#endif
    }

    void stop() {

    }
};

/**
 * Used to transfer the callback info into the tcp server thread, to avoid blocking
 * the network thread.
 */
struct socket_message_t
{
    enum event
    {
        message,
        connect,
        disconnect,
        quit,
    };

    wiced_tcp_socket_t*  socket;
    event event_type;
};


/**
 * A threaded TCP server that delegates to the SimpleProtocolDispatcher
 */
class TCPServerDispatcher
{
    SimpleProtocolDispatcher&   dispatcher_;
    wiced_interface_t           iface_;
    wiced_thread_t              thread_;
    wiced_queue_t               queue_;
    wiced_tcp_server_t          server_;

    /**
     * The callbacks from the tcp_server don't take a data argument, so we're forced to
     * resort to globals. No biggie - we don't need more than one tcp server.
     */
    static TCPServerDispatcher*  static_server;

    /**
     * Creates a stream for the client socket, wraps this in a reader/writer
     * and delegates to the dispatcher to handle the incoming command and produce the
     * result.
     * @param client
     */
    void handle_client(wiced_tcp_socket_t& client) {
        wiced_tcp_stream_t stream;
        if (!wiced_tcp_stream_init(&stream, &client)) {
            Reader r; Writer w;
            tcp_stream_writer(w, &stream);
            tcp_stream_reader(r, &stream);
            dispatcher_.handle(r, w);
            wiced_tcp_stream_flush(&stream);
            wiced_tcp_stream_deinit(&stream);
            wiced_tcp_server_disconnect_socket(&server_, &client);
        }
    }

    static wiced_result_t connect_callback(wiced_tcp_socket_t* socket, void* data) {
        return post_event(socket_message_t::connect, socket);
    }

    static wiced_result_t disconnect_callback(wiced_tcp_socket_t* socket, void* data) {
        return post_event(socket_message_t::disconnect, socket);
    }

    static wiced_result_t receive_callback(wiced_tcp_socket_t* socket, void* data) {
        return post_event(socket_message_t::message, socket);
    }

    static wiced_result_t post_event(socket_message_t::event event_type, wiced_tcp_socket_t* socket)
    {
        socket_message_t message;
        message.socket = socket;
        message.event_type = event_type;
        if (static_server)
            wiced_rtos_push_to_queue(&static_server->queue_, &message, WICED_NO_WAIT);
        return WICED_SUCCESS;
    }

public:

    TCPServerDispatcher(SimpleProtocolDispatcher& dispatcher, wiced_interface_t iface)
        : dispatcher_(dispatcher), iface_(iface)
    {
        memset(&thread_, 0, sizeof(thread_));
        memset(&server_, 0, sizeof(server_));
    }

    void start()
    {
        static_server = this;

        if (wiced_rtos_init_queue(&queue_, NULL, sizeof(socket_message_t), 10))
            return;

        if (wiced_tcp_server_start(&server_, iface_, 5609, 5, connect_callback, receive_callback, disconnect_callback, NULL))
            return;

        wiced_rtos_create_thread(&thread_, WICED_DEFAULT_LIBRARY_PRIORITY, "tcp server", tcp_server_thread, 1024*6, this);
    }

    void stop() {
        post_event(socket_message_t::quit, NULL);

        if ( wiced_rtos_is_current_thread( &thread_ ) != WICED_SUCCESS )
        {
            wiced_rtos_thread_force_awake( &thread_ );
            wiced_rtos_thread_join( &thread_);
            wiced_rtos_delete_thread( &thread_ );
        }

        wiced_tcp_server_stop(&server_);
        wiced_rtos_deinit_queue(&queue_);
        static_server = NULL;
        WPRINT_APP_INFO( ( "TCP client done\n" ) );
    }

    bool handle_message(socket_message_t& event)
    {
        bool quit = false;
        switch(event.event_type)
        {
          case socket_message_t::disconnect:
              wiced_tcp_server_disconnect_socket(&server_, event.socket);
              break;

          case socket_message_t::connect:
              wiced_tcp_server_accept(&server_, event.socket);
              break;

          case socket_message_t::message:
              handle_client(*event.socket);
              break;

          case socket_message_t::quit:
              quit = true;
              break;
          }
        return quit;
    }

    void run() {
        bool quit = false;
        for (;!quit;)
        {
            socket_message_t event;
            if (wiced_rtos_pop_from_queue(&queue_, &event, WICED_NEVER_TIMEOUT))
                break;

            handle_message(event);
        }
        WPRINT_APP_INFO( ( "TCP server exiting\n" ) );
    }

    /**
     * Function that is main entry point for the tcpserver thread. Just bounces the call
     * back to the run() method.
     */
    static void tcp_server_thread(uint32_t value) {
        TCPServerDispatcher* dispatcher = (TCPServerDispatcher*)value;
        dispatcher->run();
        WICED_END_OF_CURRENT_THREAD( );
    }
};

TCPServerDispatcher*  TCPServerDispatcher::static_server = NULL;

/**
 * The SoftAP setup application. This co-ordinates the various dispatchers and the soft AP.
 */
class SoftAPApplication
{
    SoftAPController softAP;
    AllSoftAPCommands commands;
#if SOFTAP_HTTP
    HTTPDispatcher http;
#endif
    SimpleProtocolDispatcher simpleProtocol;
    TCPServerDispatcher tcpServer;
    SerialDispatcher serial;

public:
    SoftAPApplication(void (*complete_callback)()) :
            commands(&softAP.complete_semaphore(), complete_callback),
#if SOFTAP_HTTP
                    http(commands),
#endif
            simpleProtocol(commands),
            tcpServer(simpleProtocol, WICED_AP_INTERFACE),
            serial(simpleProtocol)
    {
        softAP.start();
        serial.start();
        tcpServer.start();
#if SOFTAP_HTTP
        http.start();
#endif
    }

    ~SoftAPApplication()
    {
#if SOFTAP_HTTP
        http.stop();
#endif
        tcpServer.stop();
        serial.stop();
        softAP.stop();
    }
};

softap_handle softap_start(softap_config* config) {
    SoftAPApplication* app = new SoftAPApplication(config->softap_complete);
    return app;
}

void softap_stop(softap_handle handle) {
    SoftAPApplication* app = (SoftAPApplication*)handle;
    delete app;
}
