studiohsoftware/2WIRELESS/Firmware/photon/PhotonCore/core_hal.h

/**
 ******************************************************************************
 * @file    core_hal.h
 * @author  Satish Nair, Brett Walach
 * @version V1.0.0
 * @date    12-Sept-2014
 * @brief
 ******************************************************************************
  Copyright (c) 2013-2015 Particle Industries, Inc.  All rights reserved.

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
  You should have received a copy of the GNU Lesser General Public
  License along with this library; if not, see <http://www.gnu.org/licenses/>.
 ******************************************************************************
 */

/* Define to prevent recursive inclusion -------------------------------------*/
#ifndef __CORE_HAL_H
#define __CORE_HAL_H

#include <stdint.h>
#include <stdbool.h>
#include <stddef.h>

/* Exported types ------------------------------------------------------------*/
typedef enum
{
    BKP_DR_01 = 0x01,
    BKP_DR_02 = 0x02,
    BKP_DR_03 = 0x03,
    BKP_DR_04 = 0x04,
    BKP_DR_05 = 0x05,
    BKP_DR_06 = 0x06,
    BKP_DR_07 = 0x07,
    BKP_DR_08 = 0x08,
    BKP_DR_09 = 0x09,
    BKP_DR_10 = 0x0a
} BKP_DR_TypeDef;

typedef enum
{
    PIN_RESET = 0x01,
    SOFTWARE_RESET = 0x02,
    WATCHDOG_RESET = 0x03,
    POWER_MANAGEMENT_RESET = 0x04,
    POWER_DOWN_RESET = 0x05,
    POWER_BROWNOUT_RESET = 0x06
} RESET_TypeDef;

// Reason codes are exposed under identifier names via the cloud - ensure the mapping is
// updated for newly added reason codes
typedef enum System_Reset_Reason
{
    RESET_REASON_NONE = 0,
    RESET_REASON_UNKNOWN = 10, // Unspecified reason
    // Hardware
    RESET_REASON_PIN_RESET = 20, // Reset from the NRST pin
    RESET_REASON_POWER_MANAGEMENT = 30, // Low-power management reset
    RESET_REASON_POWER_DOWN = 40, // Power-down reset
    RESET_REASON_POWER_BROWNOUT = 50, // Brownout reset
    RESET_REASON_WATCHDOG = 60, // Watchdog reset
    // Software
    RESET_REASON_UPDATE = 70, // Successful firmware update
    RESET_REASON_UPDATE_ERROR = 80, // Generic update error
    RESET_REASON_UPDATE_TIMEOUT = 90, // Update timeout
    RESET_REASON_FACTORY_RESET = 100, // Factory reset requested
    RESET_REASON_SAFE_MODE = 110, // Safe mode requested
    RESET_REASON_DFU_MODE = 120, // DFU mode requested
    RESET_REASON_PANIC = 130, // System panic (additional data may contain panic code)
    RESET_REASON_USER = 140 // User-requested reset
} System_Reset_Reason;

/* Exported constants --------------------------------------------------------*/

//Following is normally defined via "CFLAGS += -DDFU_BUILD_ENABLE" in makefile
#ifndef DFU_BUILD_ENABLE
#define DFU_BUILD_ENABLE
#endif

/*
 * Use the JTAG IOs as standard GPIOs (D3 to D7)
 * Note that once the JTAG IOs are disabled, the connection with the host debugger
 * is lost and cannot be re-established as long as the JTAG IOs remain disabled.
 */

#ifdef USE_SWD_JTAG
#define SWD_JTAG_ENABLE
#else
#ifdef USE_SWD
#define SWD_ENABLE_JTAG_DISABLE
#else
#define SWD_JTAG_DISABLE
#endif
#endif
/*
 * Use Independent Watchdog to force a system reset when a software error occurs
 * During JTAG program/debug, the Watchdog counting is disabled by debug configuration
 */
#define IWDG_RESET_ENABLE
#define TIMING_IWDG_RELOAD      1000 //1sec

/* Exported functions --------------------------------------------------------*/
#include "watchdog_hal.h"
#include "core_subsys_hal.h"
#include "interrupts_hal.h"

#ifdef __cplusplus
extern "C" {
#endif

void HAL_Core_Init(void);
void HAL_Core_Config(void);
bool HAL_Core_Validate_User_Module(void);
bool HAL_Core_Validate_Modules(uint32_t flags, void* reserved);
bool HAL_Core_Mode_Button_Pressed(uint16_t pressedMillisDuration);
void HAL_Core_Mode_Button_Reset(uint16_t button);
void HAL_Core_System_Reset(void);
void HAL_Core_Factory_Reset(void);

void HAL_Core_System_Reset_Ex(int reason, uint32_t data, void *reserved);
int HAL_Core_Get_Last_Reset_Info(int *reason, uint32_t *data, void *reserved);

/**
 * Notification from hal to the external system.
 * @param button    The button that was pressed, 0-based
 * @param state     The current state of the button.
 */
void HAL_Notify_Button_State(uint8_t button, uint8_t state);

typedef enum {
    HAL_STANDBY_MODE_FLAG_NONE = 0,
    HAL_STANDBY_MODE_FLAG_DISABLE_WKP_PIN = 1
} hal_standby_mode_flag_t;

void HAL_Core_Enter_Safe_Mode(void* reserved);
bool HAL_Core_Enter_Safe_Mode_Requested(void);
void HAL_Core_Enter_Bootloader(bool persist);
void HAL_Core_Enter_Stop_Mode(uint16_t wakeUpPin, uint16_t edgeTriggerMode, long seconds);
int HAL_Core_Enter_Stop_Mode_Ext(const uint16_t* pins, size_t pins_count, const InterruptMode* mode, size_t mode_count, long seconds, void* reserved);
void HAL_Core_Execute_Stop_Mode(void);
int HAL_Core_Enter_Standby_Mode(uint32_t seconds, uint32_t flags);
void HAL_Core_Execute_Standby_Mode(void);
int HAL_Core_Execute_Standby_Mode_Ext(uint32_t flags, void* reserved);

int HAL_Core_Enter_Panic_Mode(void* reserved);

uint32_t HAL_Core_Compute_CRC32(const uint8_t *pBuffer, uint32_t bufferSize);

typedef enum _BootloaderFlag_t {
    BOOTLOADER_FLAG_VERSION,
    BOOTLOADER_FLAG_STARTUP_MODE
} BootloaderFlag;

enum BootloaderFeaturesEnabled
{
    BL_FEATURE_SAFE_MODE = 1<<0,
    BL_FEATURE_DFU_MODE = 1<<1,
    BL_FEATURE_FACTORY_RESET = 1<<2,
    BL_BUTTON_FEATURES = (BL_FEATURE_SAFE_MODE|BL_FEATURE_DFU_MODE|BL_FEATURE_FACTORY_RESET)
};



uint16_t HAL_Bootloader_Get_Flag(BootloaderFlag flag);

//Following is currently defined in bootloader/src/core-vx/dfu_hal.c
//Move the definitions to core_hal.c and add hal as a dependency for bootloader
int32_t HAL_Core_Backup_Register(uint32_t BKP_DR);
void HAL_Core_Write_Backup_Register(uint32_t BKP_DR, uint32_t Data);
uint32_t HAL_Core_Read_Backup_Register(uint32_t BKP_DR);

void HAL_SysTick_Handler(void);

void HAL_Bootloader_Lock(bool lock);

bool HAL_Core_System_Reset_FlagSet(RESET_TypeDef resetType);


typedef struct runtime_info_t {
    uint16_t size;              /* Size of this struct. */
    uint16_t flags;             /* reserved, set to 0. */
    uint32_t freeheap;          /* Amount of guaranteed heap memory available. */
    uint32_t system_version;
    uint32_t total_init_heap;
    uint32_t total_heap;
    uint32_t max_used_heap; // The "highwater mark" for allocated space—that is, the maximum amount of space that was ever allocated.
    uint32_t user_static_ram;
    uint32_t largest_free_block_heap;
} runtime_info_t;

uint32_t HAL_Core_Runtime_Info(runtime_info_t* info, void* reserved);

extern void app_setup_and_loop();

typedef enum HAL_SystemClock
{
    SYSTEMCLOCK_PRIMARY,
    SYSTEMCLOCK_SPI
} HAL_SystemClock;

/**
 * Retrieves the
 * @param reserved
 * @return
 */
unsigned HAL_Core_System_Clock(HAL_SystemClock clock, void* reserved);


typedef enum hal_system_config_t
{
    SYSTEM_CONFIG_NONE,
    SYSTEM_CONFIG_DEVICE_KEY,
    SYSTEM_CONFIG_SERVER_KEY,

    SYSTEM_CONFIG_SOFTAP_PREFIX,
    SYSTEM_CONFIG_SOFTAP_SUFFIX,
    SYSTEM_CONFIG_SOFTAP_HOSTNAMES,
	SYSTEM_CONFIG_SOFTAP_DISABLE_BROADCAST //2WIRELESS

} hal_system_config_t;

/**
 * Sets a system configuration item.
 * @param config_item       The item to set
 * @param data              The data to set to
 * @param length            The length of the data.
 * @return      0 on success.
 */
int HAL_Set_System_Config(hal_system_config_t config_item, const void* data, unsigned length);


typedef enum HAL_Feature {
    FEATURE_RETAINED_MEMORY=1,       // [write only] retained memory on backup power
    FEATURE_WARM_START,              // [read only] set to true if previous retained memory contents are available]
    FEATURE_CLOUD_UDP,				// [read only] true if the UDP implementation should be used.
    FEATURE_RESET_INFO,              // [read/write] enables handling of last reset info (may affect backup registers)
    FEATURE_WIFI_POWERSAVE_CLOCK,	// [write only] enables/disables the WiFi powersave clock on the TESTMODE pin. This setting is persisted to the DCT.
    FEATURE_ETHERNET_DETECTION      // [read/write] enables Ethernet FeatherWing detection on boot
} HAL_Feature;

int HAL_Feature_Set(HAL_Feature feature, bool enabled);
bool HAL_Feature_Get(HAL_Feature feature);

/**
 * Externally defined function that is called before user constructors.
 */
extern void module_user_init_hook(void);

int HAL_System_Backup_Save(size_t offset, const void* buffer, size_t length, void* reserved);
int HAL_System_Backup_Restore(size_t offset, void* buffer, size_t max_length, size_t* length, void* reserved);

void HAL_Core_Button_Mirror_Pin(uint16_t pin, InterruptMode mode, uint8_t bootloader, uint8_t button, void* reserved);
void HAL_Core_Button_Mirror_Pin_Disable(uint8_t bootloader, uint8_t button, void* reserved);

void HAL_Core_Led_Mirror_Pin(uint8_t led, pin_t pin, uint32_t flags, uint8_t bootloader, void* reserved);
void HAL_Core_Led_Mirror_Pin_Disable(uint8_t led, uint8_t bootloader, void* reserved);

/**
 * HAL event type.
 */
typedef enum {
	HAL_EVENT_OUT_OF_MEMORY = 1,		   // flags are set to the size of the memory block requested.
	HAL_EVENT_GENERATE_DEVICE_KEY = 10 // Fired when HAL attempts to generate device keys

} HAL_Event;

/**
 * HAL event flags.
 */
typedef enum {
    HAL_EVENT_FLAG_START = 0x01, // Event started
    HAL_EVENT_FLAG_STOP = 0x02 // Event stopped
} HAL_Event_Flag;

typedef void(*HAL_Event_Callback)(int event, int flags, void* data);

void HAL_Set_Event_Callback(HAL_Event_Callback callback, void* reserved);

#ifdef __cplusplus
}
#endif

#endif  /* __CORE_HAL_H */
